carolparedesf/arroyo-mburicao-estacion-lluvia/docs/preliminary_results/Sensor_optico_lluvia.jpg

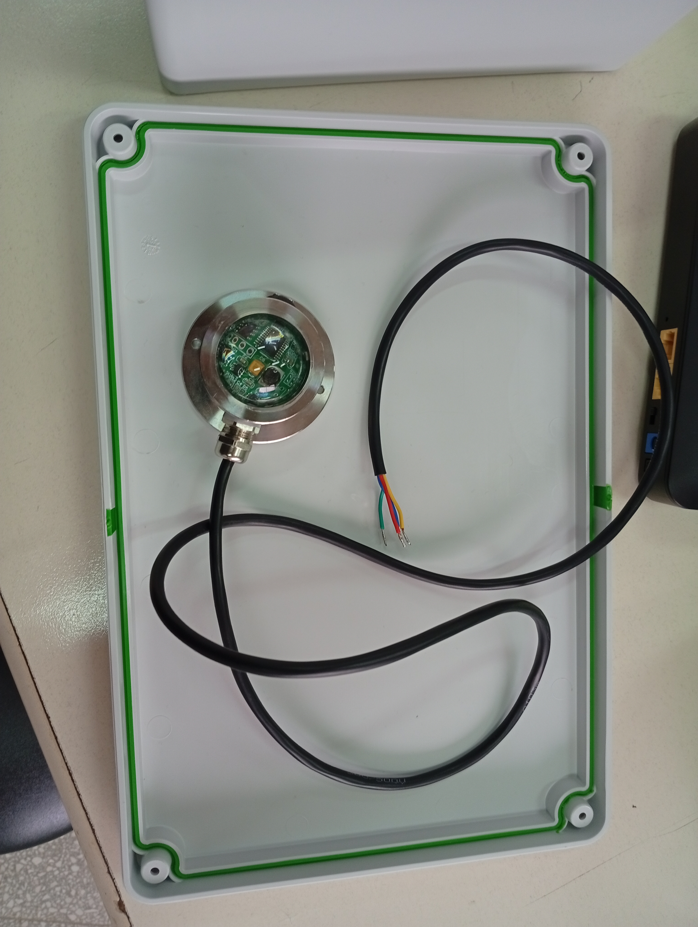
docs/preliminary_results/Sensor_optico_lluvia.jpg
