carolparedesf/arroyo-mburicao-estacion-lluvia/docs/preliminary_results/Caja_contenedora.jpg

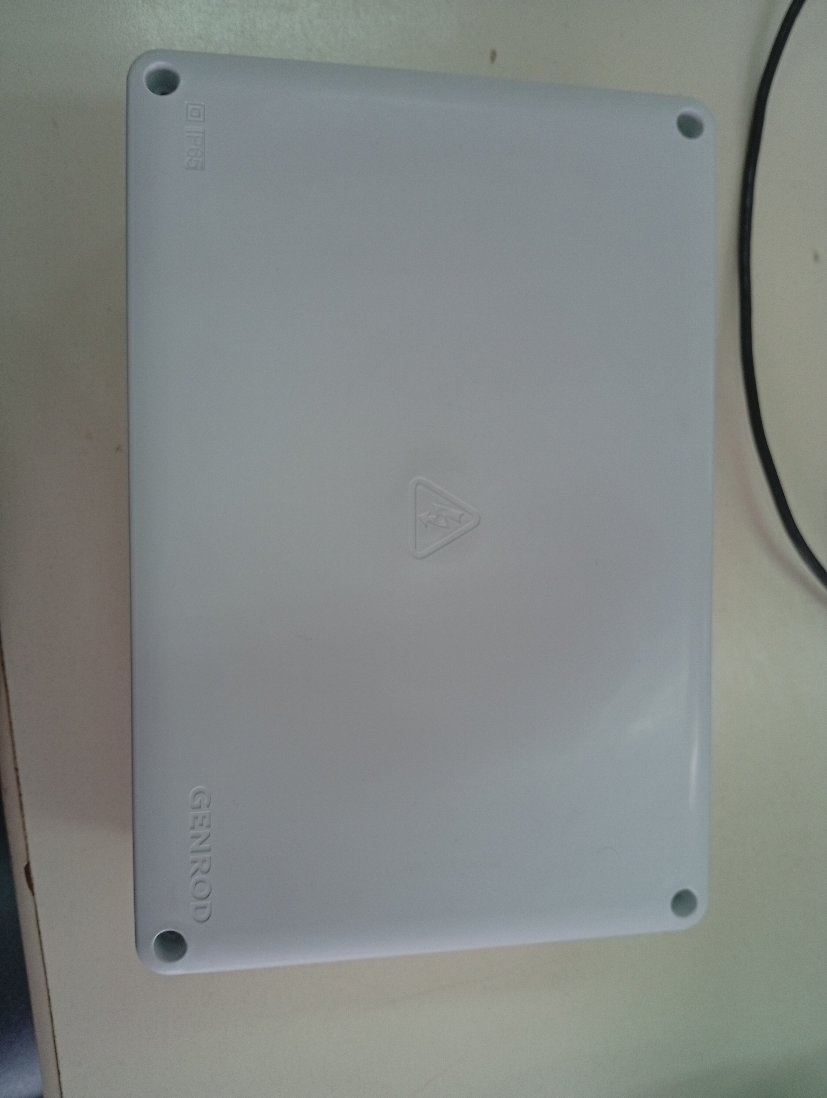
docs/preliminary_results/Caja_contenedora.jpg
