carolparedesf/arroyo-mburicao-estacion-lluvia/docs/preliminary_results/Prueba_Base_datos.jpg

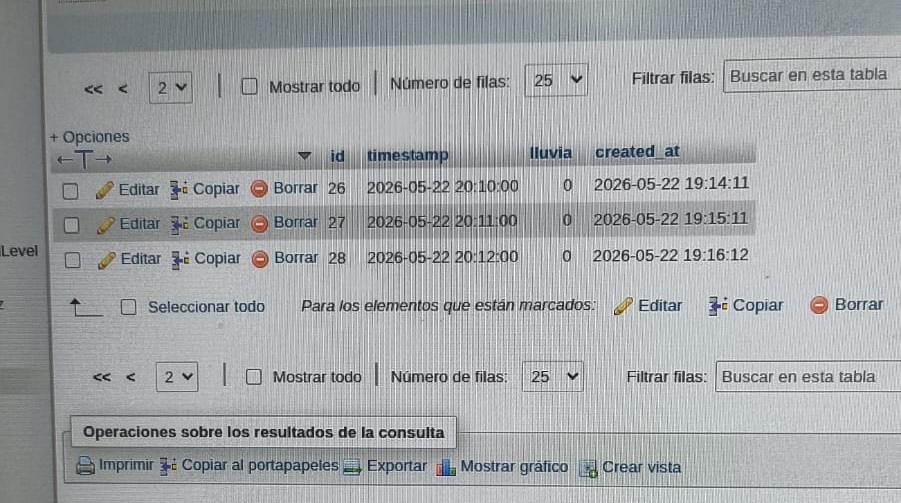
docs/preliminary_results/Prueba_Base_datos.jpg
