carolparedesf/arroyo-mburicao-estacion-lluvia/docs/preliminary_results/Prueba_conjunta.jpg

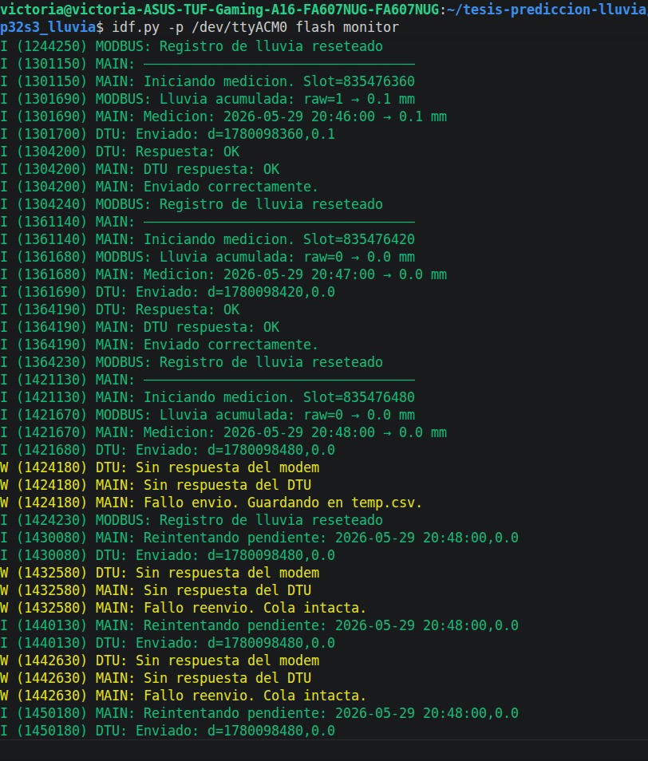
docs/preliminary_results/Prueba_conjunta.jpg
