carolparedesf/arroyo-mburicao-estacion-lluvia/docs/preliminary_results/prueba_debug.jpg

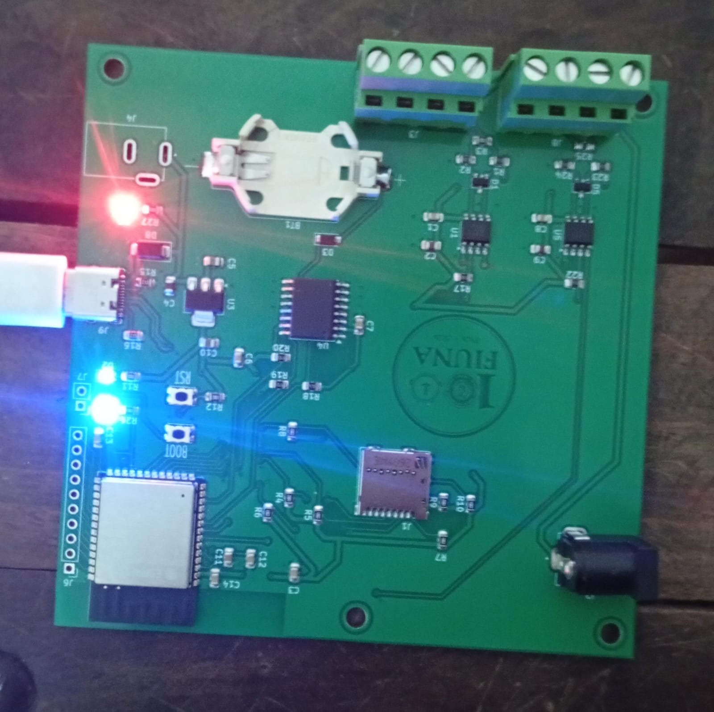
docs/preliminary_results/prueba_debug.jpg
