carolparedesf/arroyo-mburicao-estacion-lluvia/docs/preliminary_results/Prueba_Envio.jpg

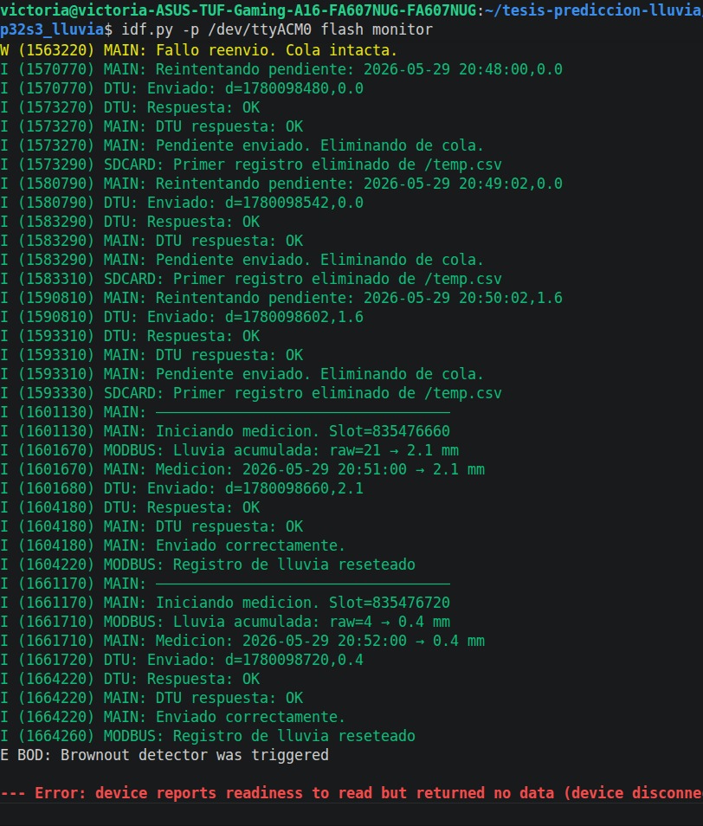
docs/preliminary_results/Prueba_Envio.jpg
