carolparedesf/arroyo-mburicao-estacion-lluvia/docs/preliminary_results/Prueba_RTC.jpg

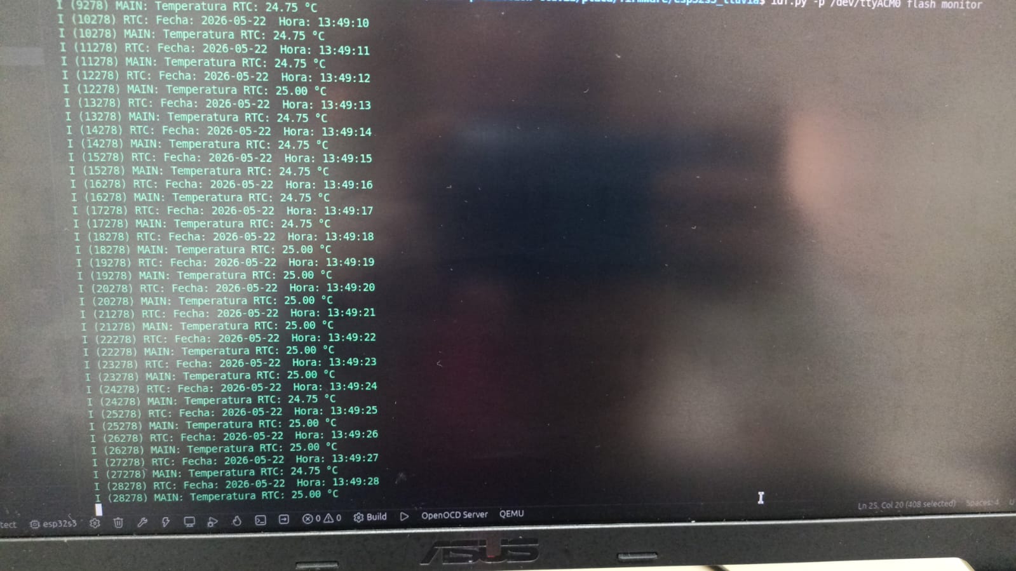
docs/preliminary_results/Prueba_RTC.jpg
