carolparedesf/arroyo-mburicao-estacion-lluvia/docs/preliminary_results/Prueba_Sensores.jpg

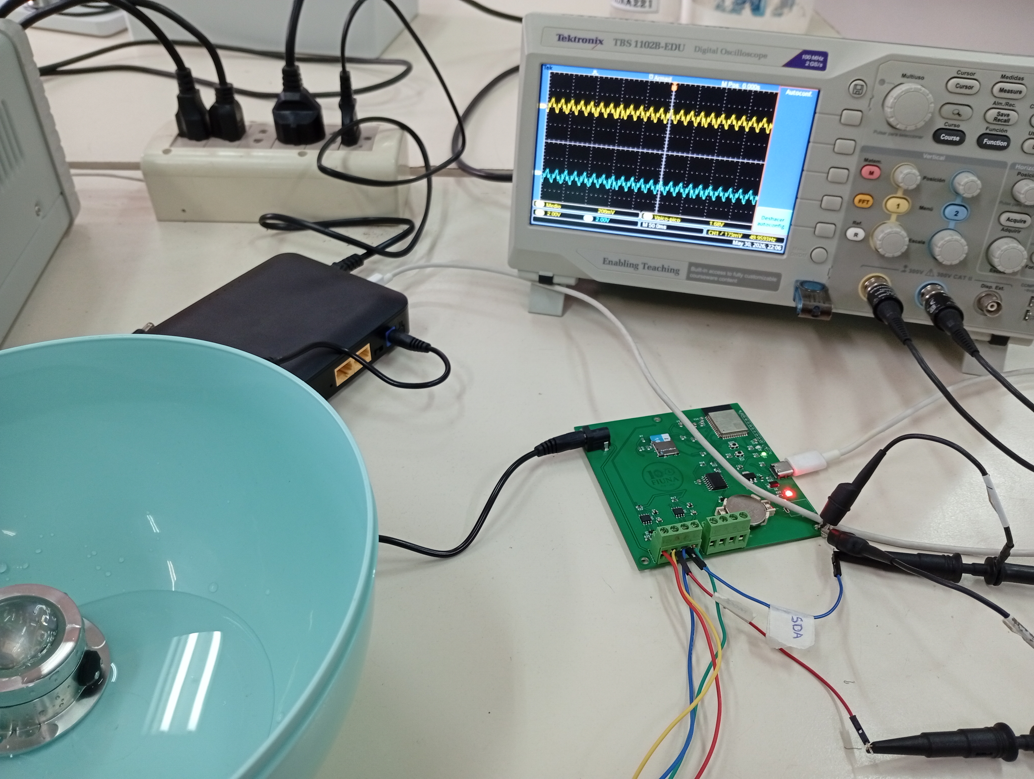
docs/preliminary_results/Prueba_Sensores.jpg
