carolparedesf/arroyo-mburicao-estacion-lluvia/docs/preliminary_results/Voltaje_Diferencia_AyB.jpg

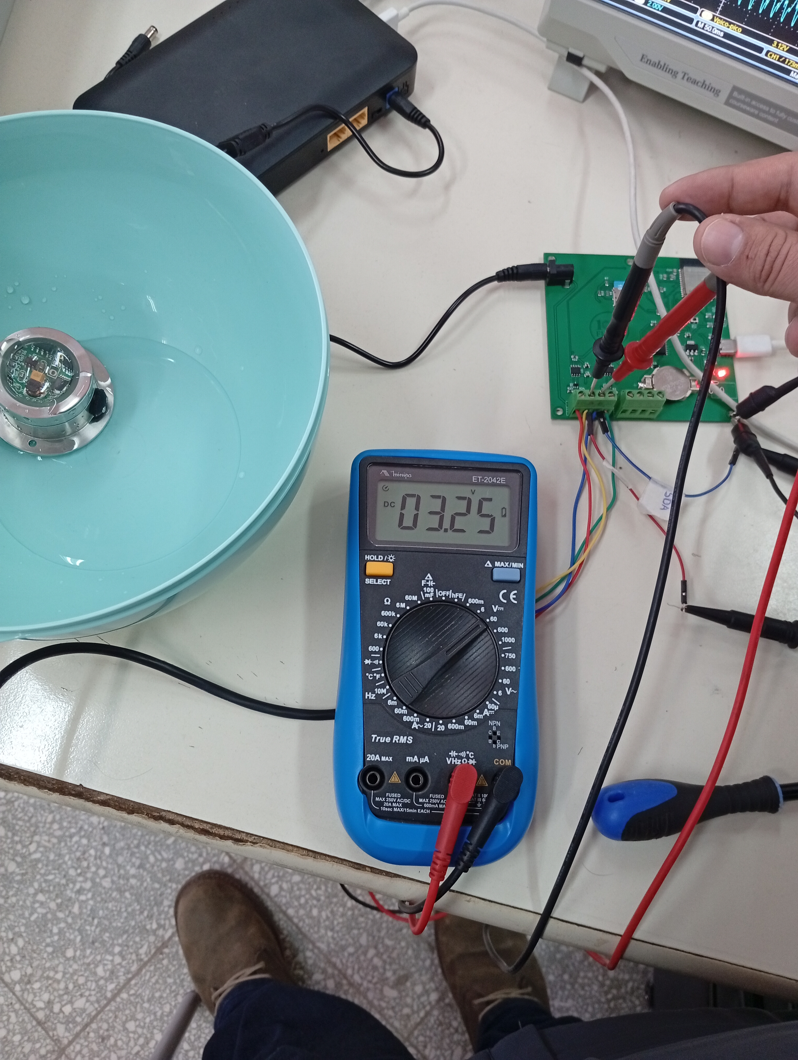
docs/preliminary_results/Voltaje_Diferencia_AyB.jpg
